eduardofv/medidor-co2/doc/assets/photos/IMG_8085.JPG

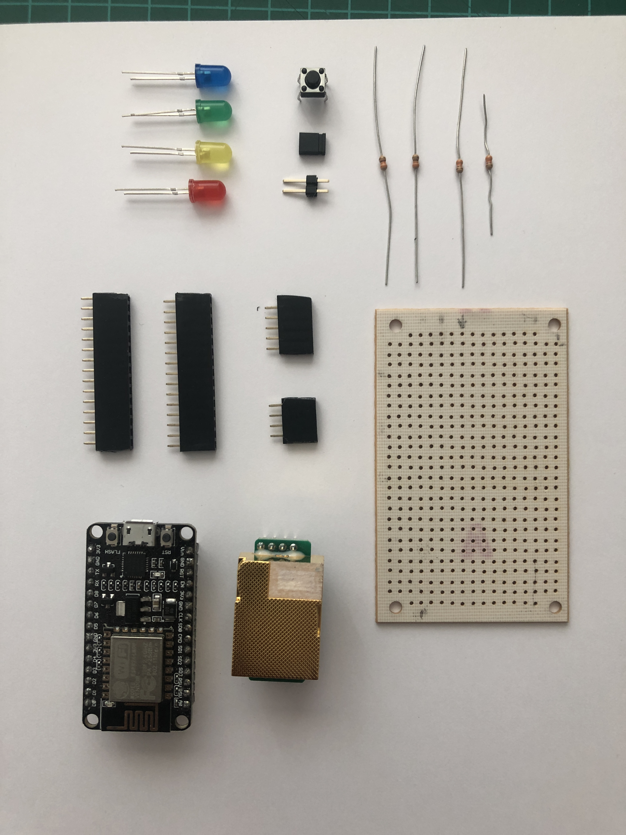
doc/assets/photos/IMG_8085.JPG
