eduardofv/medidor-co2/doc/assets/photos/IMG_8086.JPG

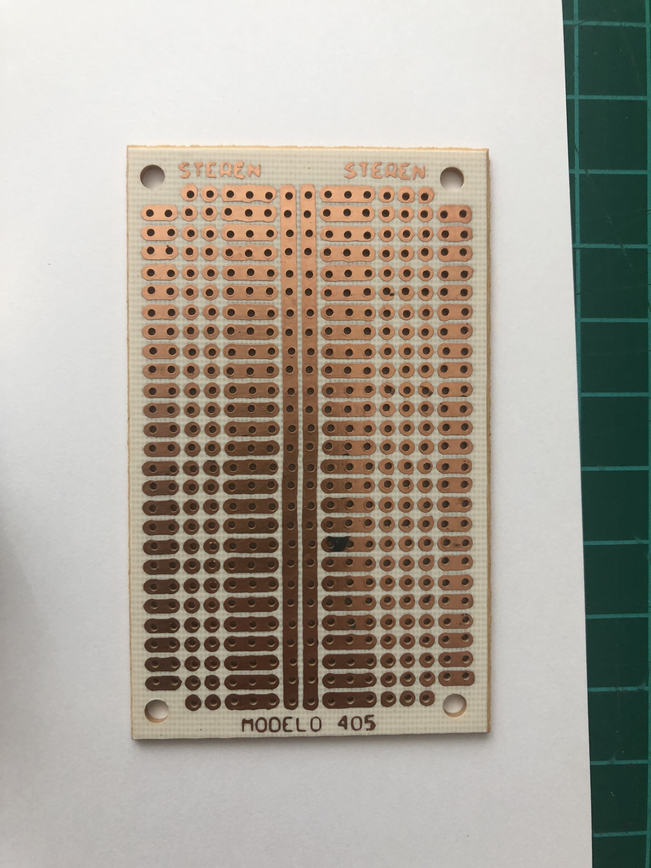
doc/assets/photos/IMG_8086.JPG
