eduardofv/medidor-co2/doc/assets/photos/IMG_8087.JPG

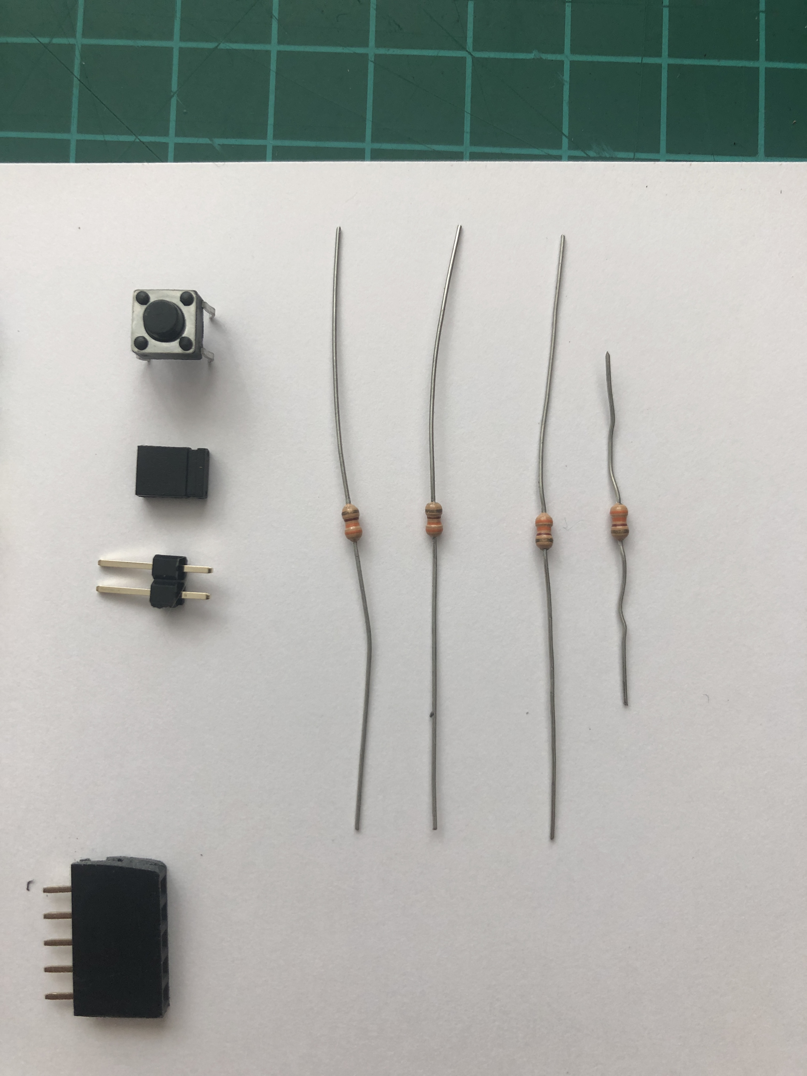
doc/assets/photos/IMG_8087.JPG
