eduardofv/medidor-co2/doc/assets/photos/IMG_8088.JPG

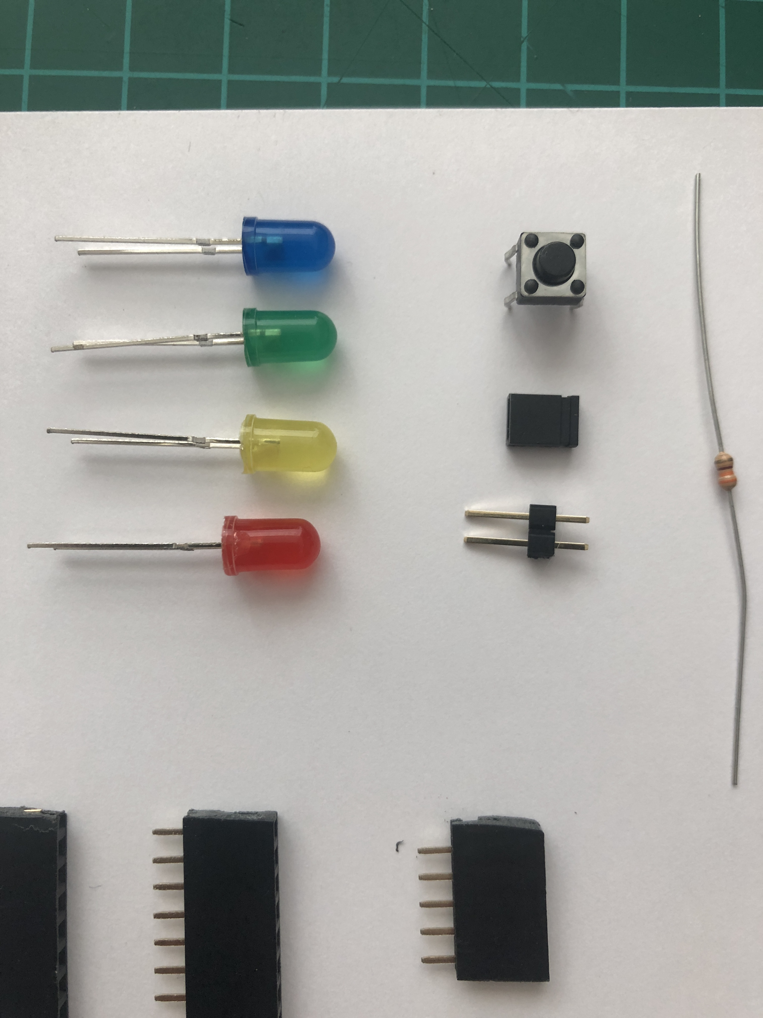
doc/assets/photos/IMG_8088.JPG
