eduardofv/medidor-co2/doc/assets/photos/IMG_8089.JPG

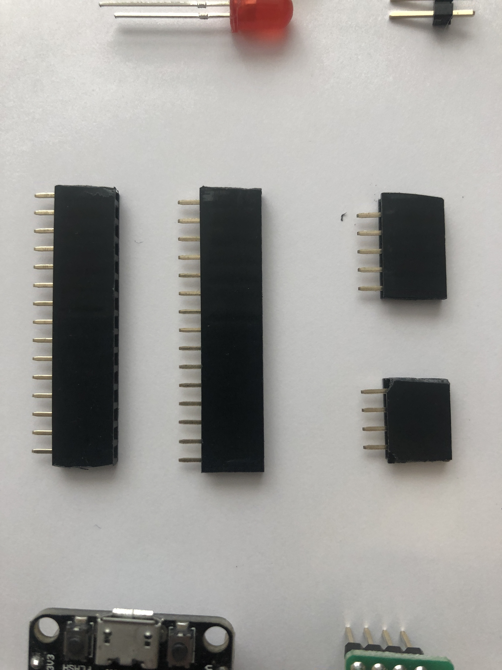
doc/assets/photos/IMG_8089.JPG
