eduardofv/medidor-co2/doc/assets/photos/IMG_8090.JPG

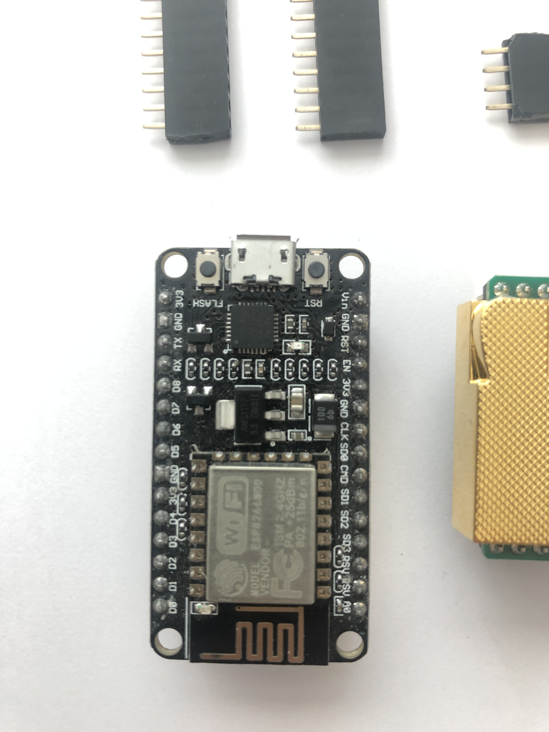
doc/assets/photos/IMG_8090.JPG
