eduardofv/medidor-co2/doc/assets/photos/IMG_8091.JPG

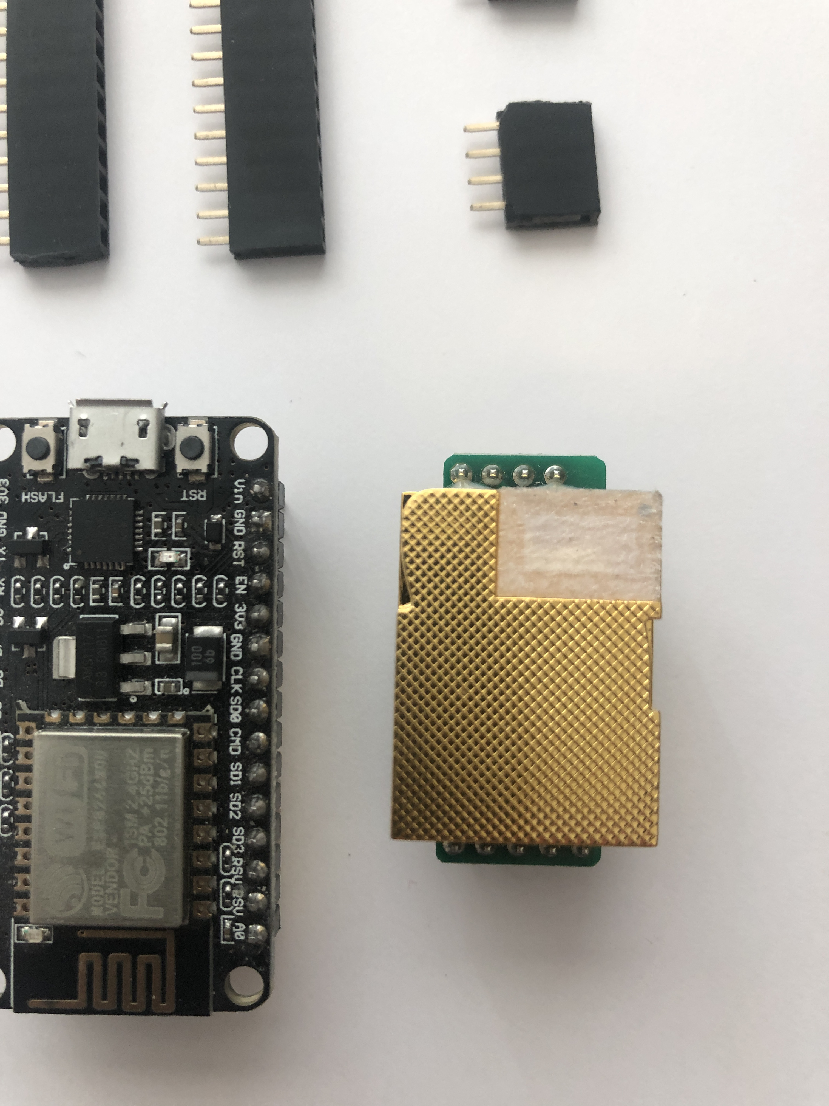
doc/assets/photos/IMG_8091.JPG
