eduardofv/medidor-co2/doc/assets/photos/IMG_8092.JPG

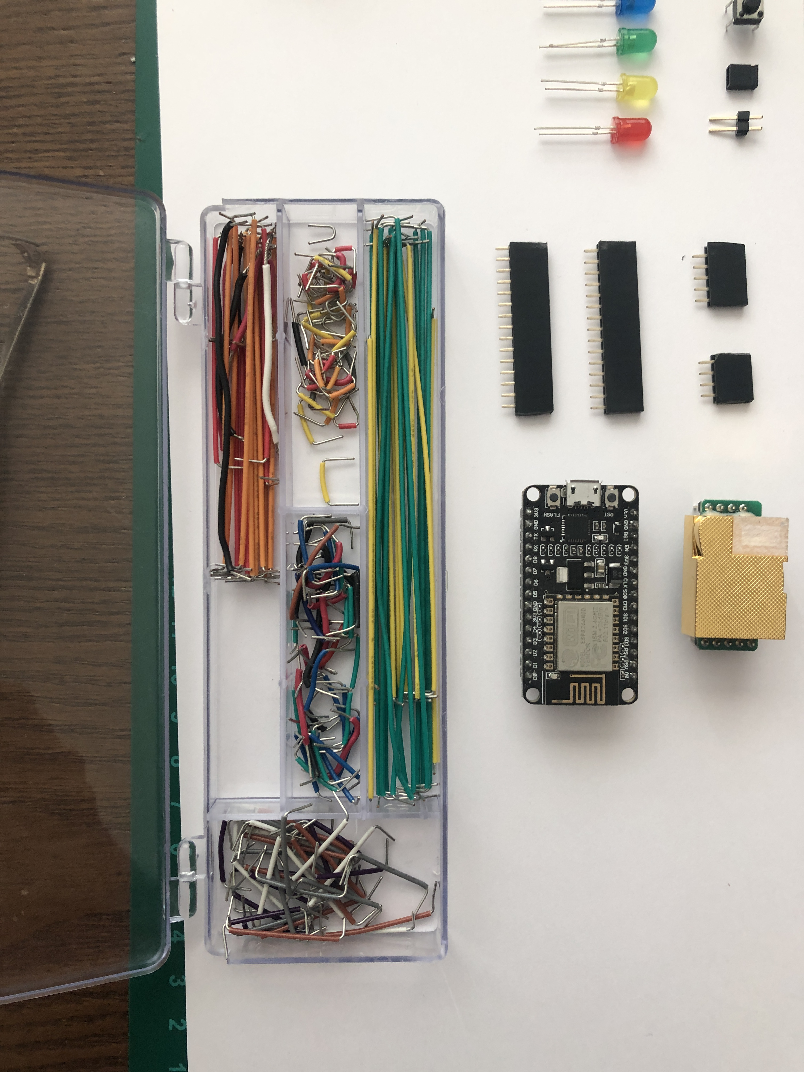
doc/assets/photos/IMG_8092.JPG
