eduardofv/medidor-co2/doc/assets/photos/IMG_8093.JPG

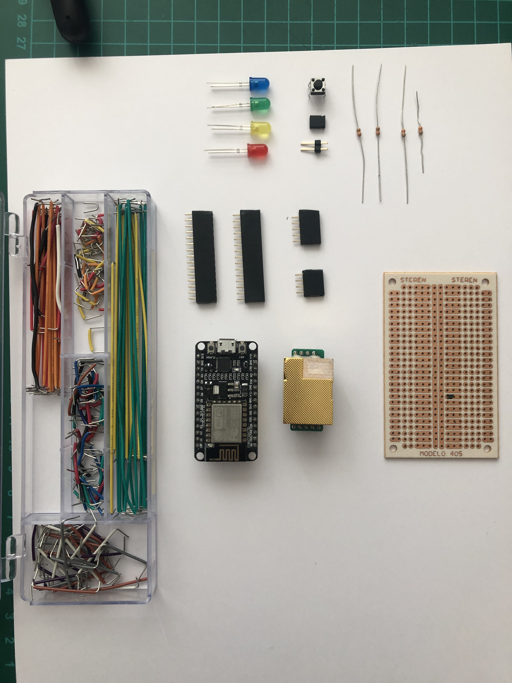
doc/assets/photos/IMG_8093.JPG
