eduardofv/medidor-co2/doc/assets/photos/IMG_8096.JPG

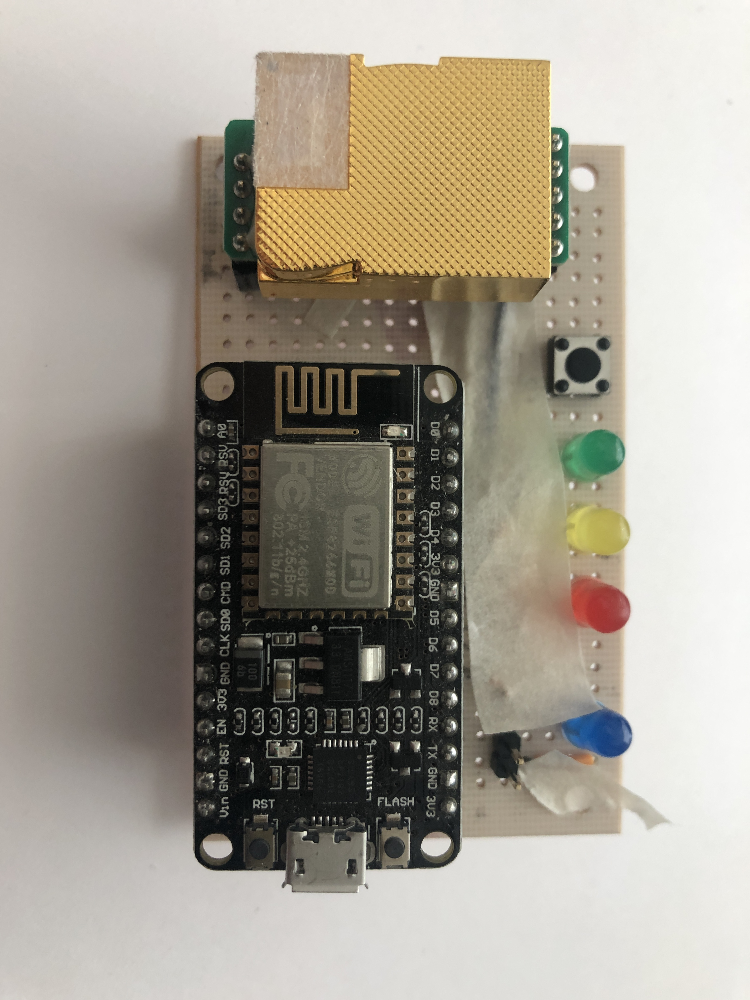
doc/assets/photos/IMG_8096.JPG
