eduardofv/medidor-co2/doc/assets/photos/IMG_8081.JPG

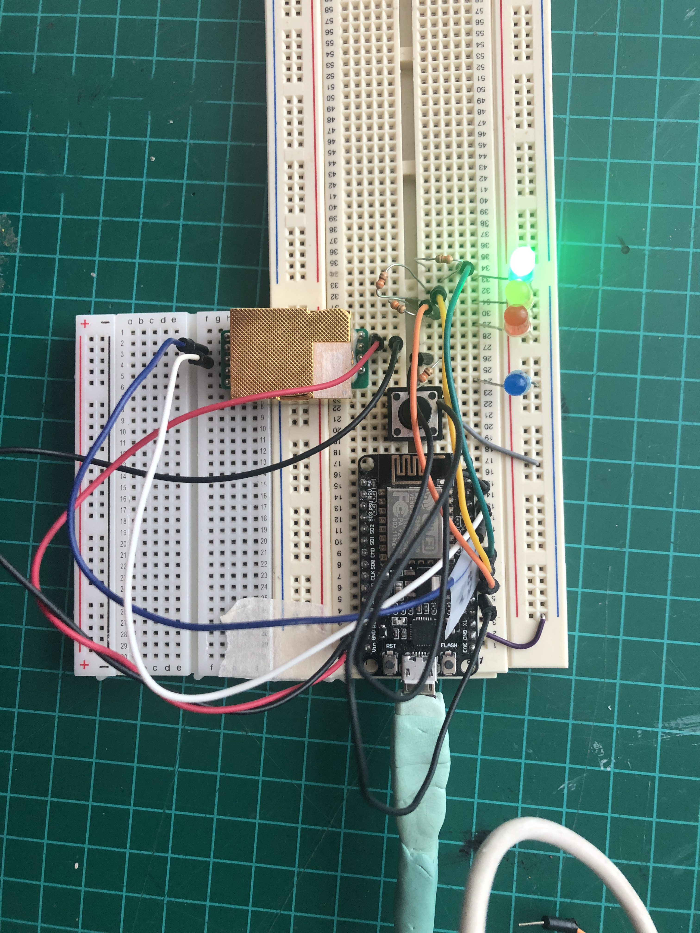
doc/assets/photos/IMG_8081.JPG
