eduardofv/medidor-co2/doc/assets/photos/IMG_8082.JPG

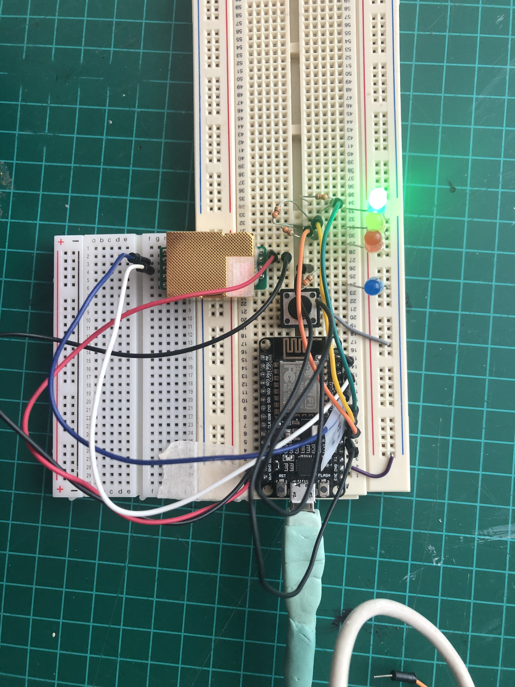
doc/assets/photos/IMG_8082.JPG
